theb0b12/caeseura/photos/IMG_7705(1).jpeg

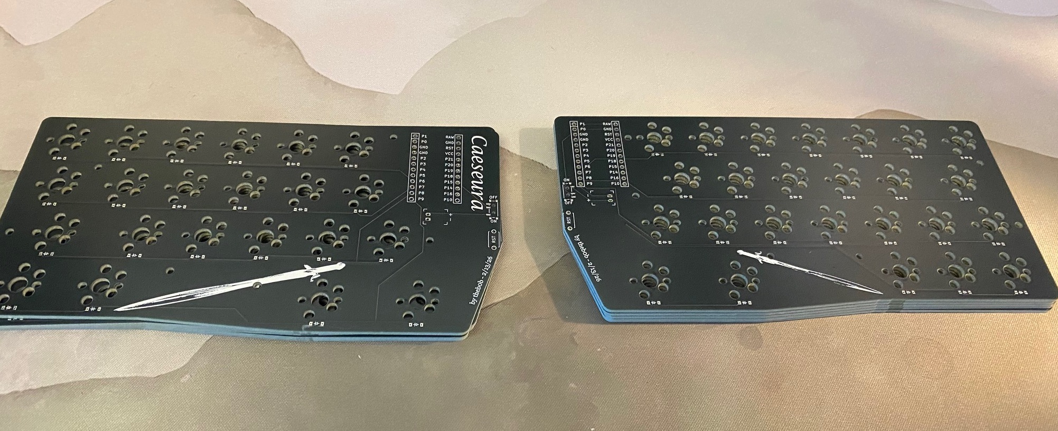
photos/IMG_7705(1).jpeg
