theb0b12/caeseura/photos/IMG_7705.jpeg

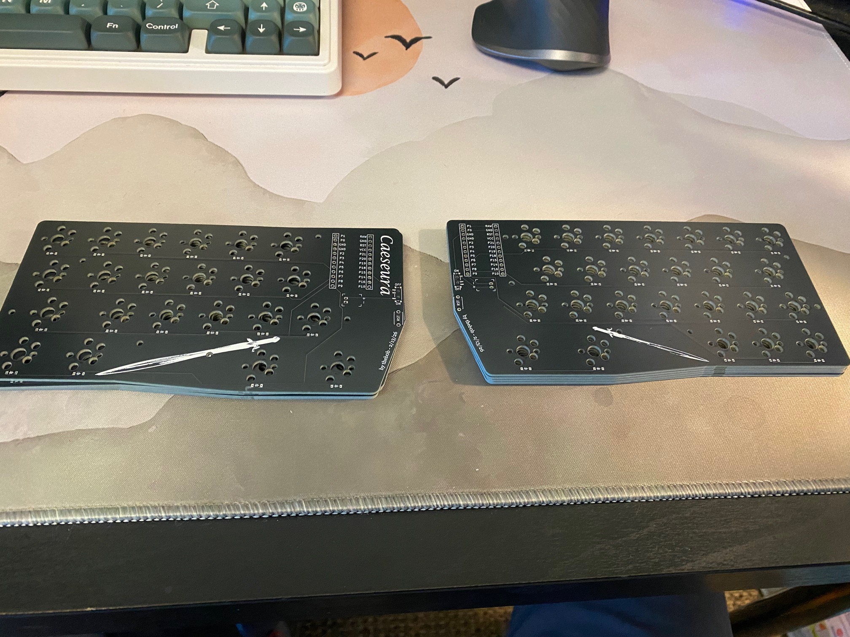
photos/IMG_7705.jpeg
