theb0b12/caeseura/photos/IMG_7722.jpeg

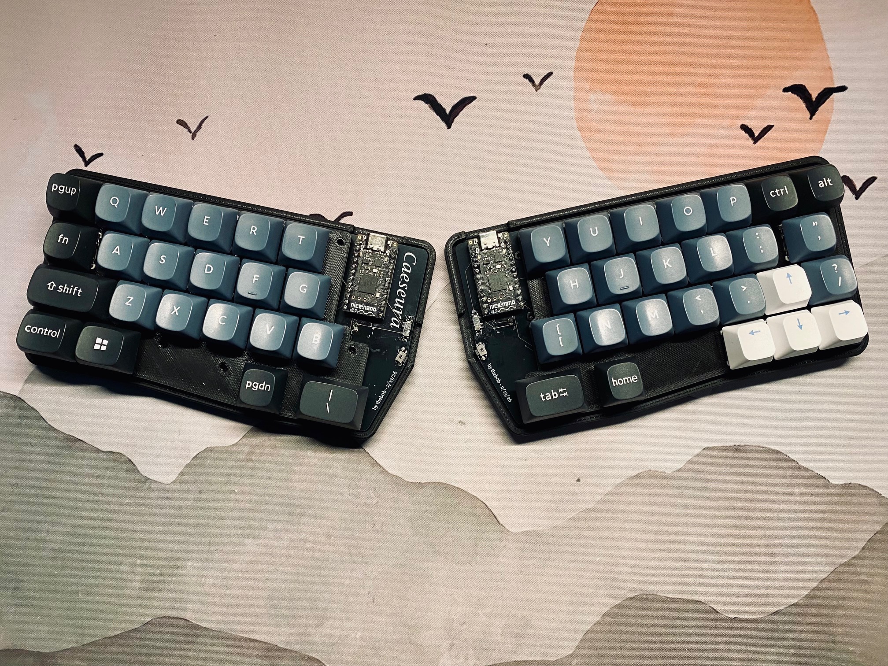
photos/IMG_7722.jpeg
