theb0b12/caeseura/photos/IMG_7723.jpeg

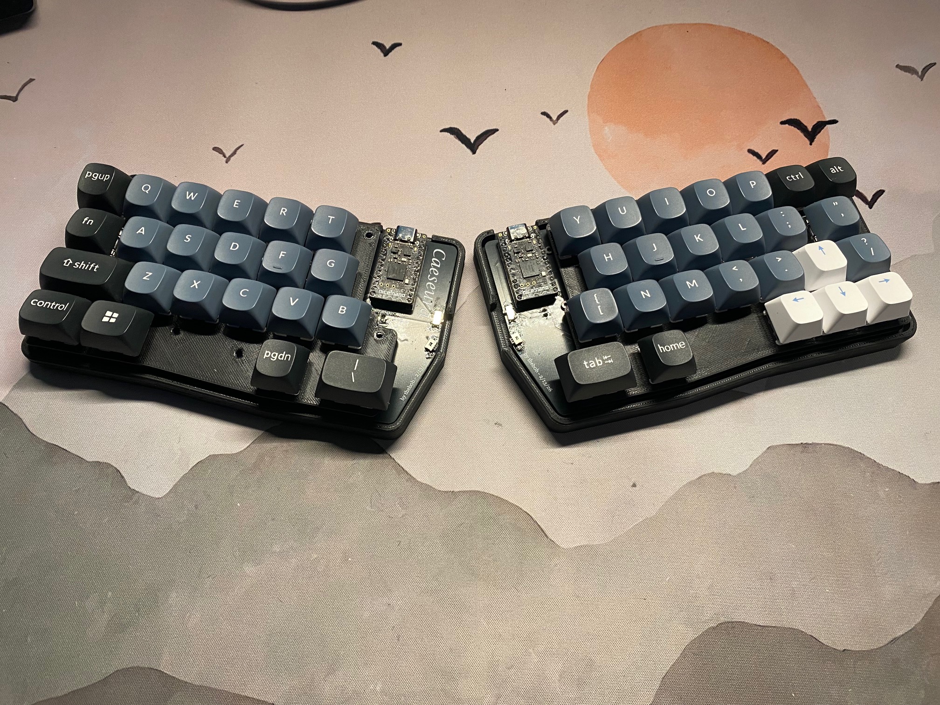
photos/IMG_7723.jpeg
