theb0b12/caeseura/photos/IMG_7724.jpeg

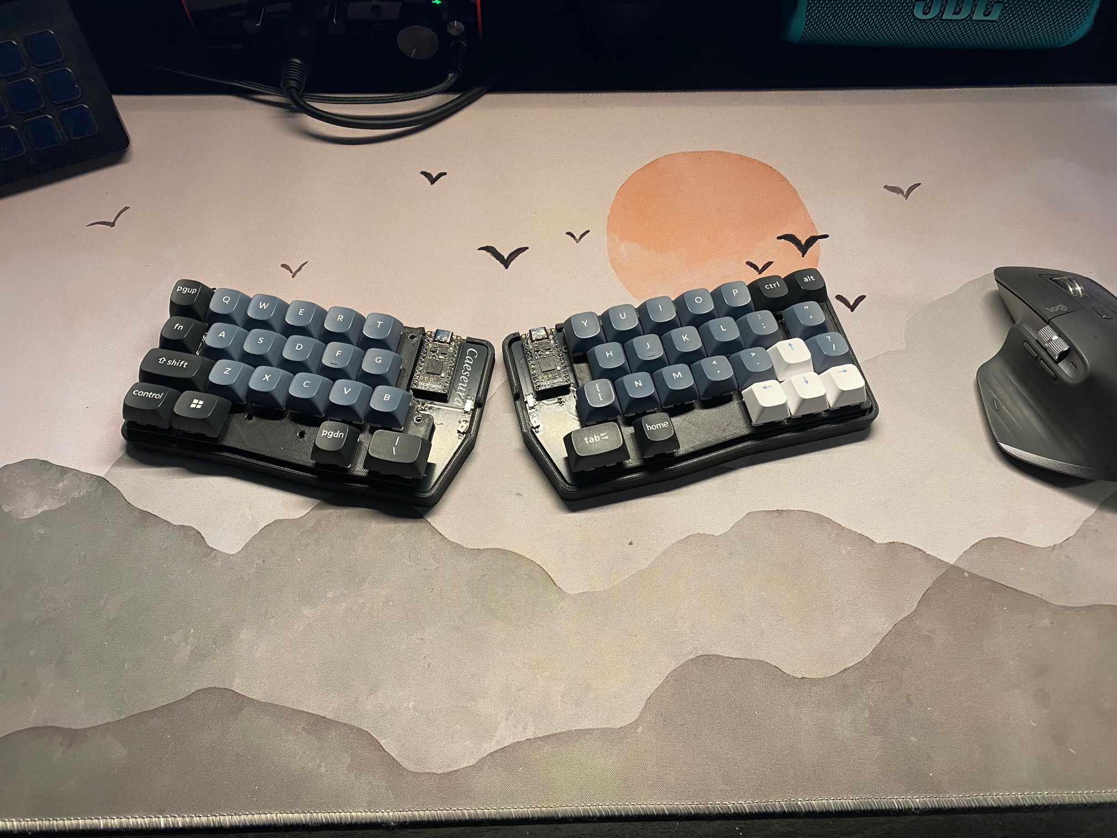
photos/IMG_7724.jpeg
