theb0b12/caeseura/cases/right/switch_plate (2).dxf

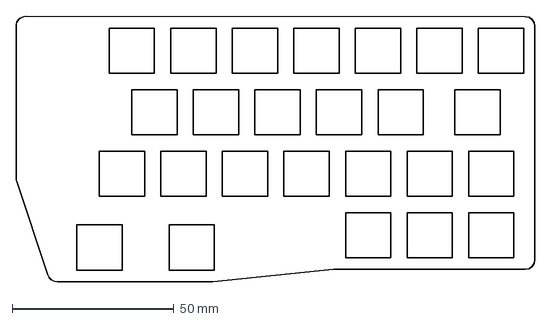
[picture p29: CAD file, 2026-03-13]
cases/right/switch_plate (2).dxf
160.2 x 81.9 mm
