theb0b12/caeseura/cases/left/xlBoard.dxf

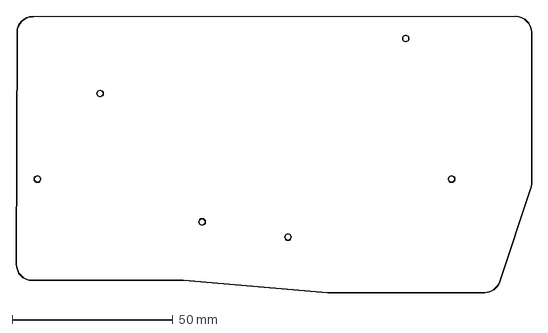
[picture p30: CAD file, 2026-03-13]
cases/left/xlBoard.dxf
160.2 x 85.9 mm
