theb0b12/caeseura/cases/left/wall_outline.dxf

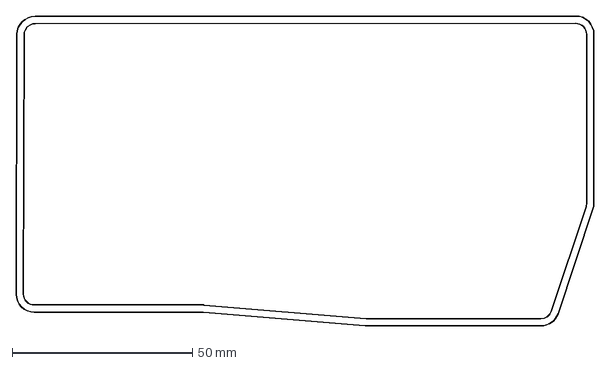
[picture p31: CAD file, 2026-03-13]
cases/left/wall_outline.dxf
160.2 x 85.9 mm
