theb0b12/caeseura/cases/left/realBoard.dxf

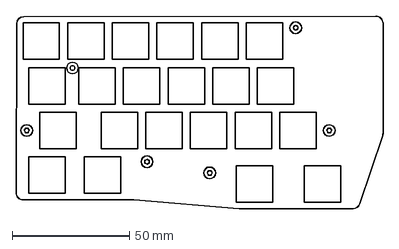
[picture p32: CAD file, 2026-03-13]
cases/left/realBoard.dxf
156.2 x 81.9 mm
