theb0b12/caeseura/pcbs/left_pcbv2.kicad_pcb

## KiCad design pcbs/left_pcbv2.kicad_pcb (2026-05-01)

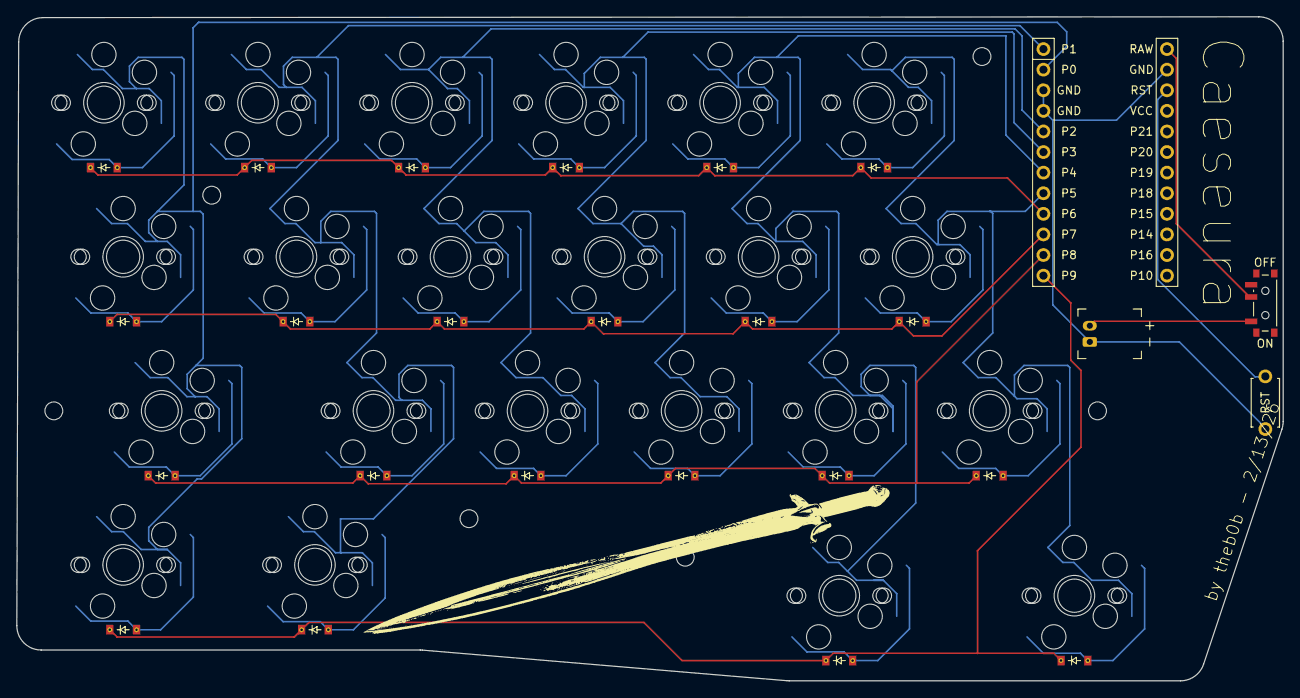
[picture p33: board left_pcbv2.kicad_pcb from above]

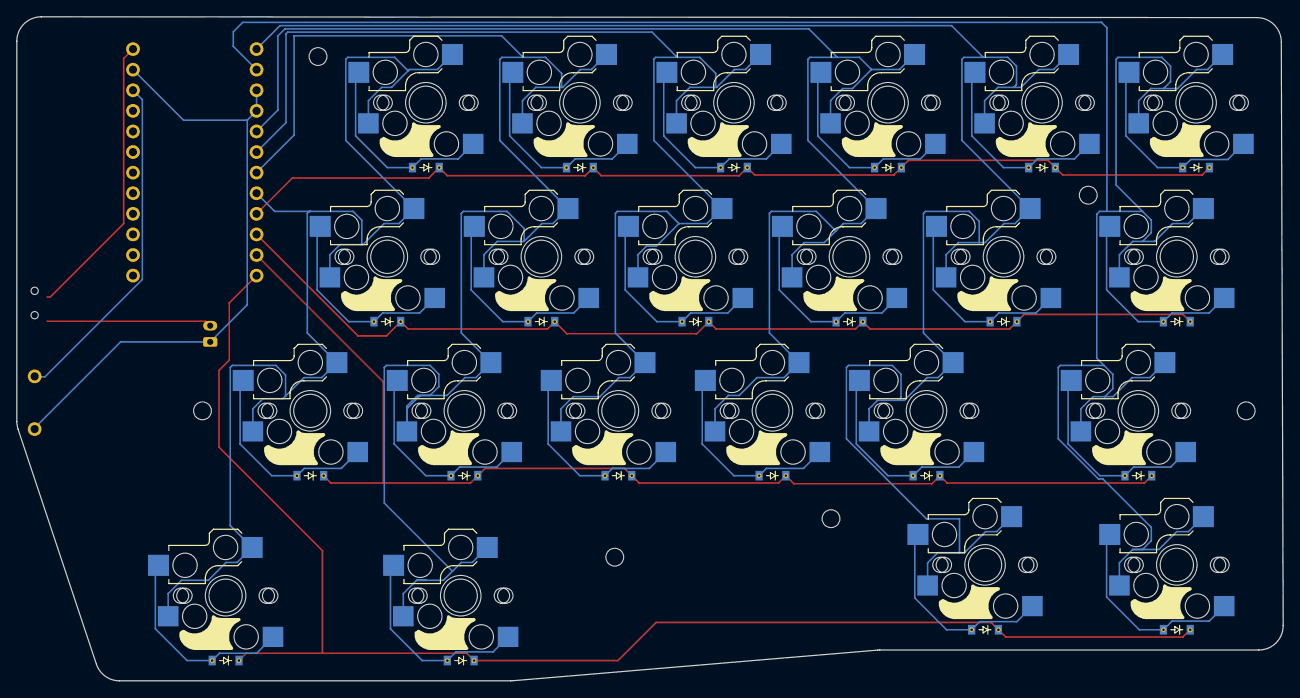
[picture p34: board left_pcbv2.kicad_pcb from below]

Board: 2 copper layers, 156.2 x 81.9 mm, 76 parts (44 on the bottom side), 36 nets.

Parts:
D1, D2, D3, D4, D5, D6, D7, D8, D9, D10, D11, D12, D13, D14, D15, D16, D17, D18, D19, D20, D21, D22: ComboDiode
JST1: battery_connector_jst_ph_2
MCU1: mcu_nice_nano
MH1, MH2, MH3, MH4, MH5, MH6: mounting_hole_npth
PWR1: power_switch_smd_side
RST1: reset_switch_tht_top
S1, S2, S3, S4, S5, S6, S7, S8, S9, S10, S11, S12, S13, S14, S15, S16, S17, S18, S19, S20, S21, S22: switch_choc_v1_v2
S23, S24, S25, S26, S27, S28, S29, S30, S31, S32, S33, S34, S35, S36, S37, S38, S39, S40, S41, S42, S43, S44: switch_mx

Connections:
BAT_P: JST1.2, PWR1.1
GND: JST1.1, MCU1.2, MCU1.21, MCU1.22, RST1.2
P0: MCU1.23, S1.1, S7.1, S13.1, S19.1, S23.1, S29.1, S35.1, S41.1
P1: MCU1.24, S2.1, S8.1, S14.1, S20.1, S24.1, S30.1, S36.1, S42.1
P2: MCU1.20, S3.1, S9.1, S15.1, S25.1, S31.1, S37.1
P3: MCU1.19, S4.1, S10.1, S16.1, S26.1, S32.1, S38.1
P4: MCU1.18, S5.1, S11.1, S17.1, S21.1, S27.1, S33.1, S39.1, S43.1
P5: MCU1.17, S6.1, S12.1, S18.1, S22.1, S28.1, S34.1, S40.1, S44.1
P6: D1.1, D2.1, D3.1, D4.1, D5.1, D6.1, MCU1.16
P7: D7.1, D8.1, D9.1, D10.1, D11.1, D12.1, MCU1.15
P8: D13.1, D14.1, D15.1, D16.1, D17.1, D18.1, MCU1.14
P9: D19.1, D20.1, D21.1, D22.1, MCU1.13
RAW: MCU1.1, PWR1.2
RST: MCU1.3, RST1.1
a_default: D8.1, D8.2, S8.2, S30.2
b_default: D18.1, D18.2, S18.2, S40.2
c_default: D16.1, D16.2, S16.2, S38.2
d_default: D10.1, D10.2, S10.2, S32.2
e_default: D4.1, D4.2, S4.2, S26.2
esc_default: D1.1, D1.2, S1.2, S23.2
f_default: D11.1, D11.2, S11.2, S33.2
g_default: D12.1, D12.2, S12.2, S34.2
lctrl_default: D19.1, D19.2, S19.2, S41.2
lower_default: D21.1, D21.2, S21.2, S43.2
lshift_default: D13.1, D13.2, S13.2, S35.2
q_default: D2.1, D2.2, S2.2, S24.2
r_default: D5.1, D5.2, S5.2, S27.2
s_default: D9.1, D9.2, S9.2, S31.2
space_default: D22.1, D22.2, S22.2, S44.2
super_default: D20.1, D20.2, S20.2, S42.2
t_default: D6.1, D6.2, S6.2, S28.2
tab_default: D7.1, D7.2, S7.2, S29.2
v_default: D17.1, D17.2, S17.2, S39.2
w_default: D3.1, D3.2, S3.2, S25.2
x_default: D15.1, D15.2, S15.2, S37.2
z_default: D14.1, D14.2, S14.2, S36.2
